WizVader/Smart-Energy-Monitor/Advance/Hardware/Comparator.asc

Cf1: cap; 1.592n
Cf2: cap; 1.592n
Cf3: cap; 1.592n
D1: diode
D2: diode
R1: res; 10k
R2: res; 10k
R3: res; 10k
R4: res; 10k
R5: res; 1k
R6: res; 500k
R7: res; 35.714k
R8: res; 1k
R9: res; 500k
R10: res; 35.714k
R11: res; 10k
R12: res; 330k
Rf1: res; 10k
Rf2: res; 10k
Rf3: res; 10k
U1: opamp2; LM324
U2: opamp2; LM324
U3: opamp2; LM324
U4: opamp2; LM324
V1: voltage; SINE(2.1 1 500); AC 1 0
V2: voltage; 5V
V3: voltage; 2.1
V4: voltage; 2.1
V5: voltage; 5
V6: voltage; 2.1
V7: voltage; 5
Named nets: 0, Vopamp, Vfilter, Vout, Voutput, 5V, Vzero, 2V1, Vvo
.tran 0 0.5 0 0.1m
.lib LM324.lib
Voltage Zero Crossing Detector Circuit using comparator
Notes:
- When Vvo > 2.1V, Vzero = 5V
When Vvo < 2.1V, Vzero = GND (Active high)
