WizVader/Smart-Energy-Monitor/Advance/Hardware/LevelShiftingAmplificationCircuit.asc

R1: res; 92.368k
R2: res; 92.368k
R3: res; 100k
R4: res; 100k
R5: res; 10k
R6: res; 10k
R7: res; 21.053k
R8: res; 21.053k
U1: opamp2; LM324
U2: opamp2; LM324
V2: voltage; 2.1V
Named nets: 0, 5V, Vvs, Vvo, 2V1, Vis, Vio
Differential Ampliflier for Voltage Sensor
Power/Signal Sources
Differential Amplifier for Current Sensor
