WizVader/Smart-Energy-Monitor/Advance/Hardware/rcfilter.asc

Cf1: cap; 1.592nF
Rf1: res; 10k
Named nets: Vio, 0, Vfilter
