WizVader/Smart-Energy-Monitor/Advance/Hardware/Regulator5V.asc

Cin1: cap; 47µ; Rser=0.001
Cout1: cap; 10µ; Rser=0.001
D1: diode; 1N4148
Reg1: LT1085-5
Rin1: res; 20
RL1: res; 50
V1: voltage; 5V
Named nets: 0, Vac, 5V, Vin, 5VDis
Notes: 
- Change net label 5VDis to 5V to use the DC regulator - In this case 
  the 5V net attached to V1 needs to be set to 5VDis to disconnect it
