WizVader/Smart-Energy-Monitor/Advance/Hardware/Sensor_Circtuits.asc

Lload1: ind; 4mH
Ra1: res; 498k
Rb1: res; 24k
Rload1: res; 94.026
Rs1: res; 0.5645
Vsupply1: voltage; SINE(0 21.778 500)
Named nets: 0, Vac, Vis, Vvs
Load 
(2.5VA-7.5VA)
Current Sens 
(Pmax=?)
