WizVader/Smart-Energy-Monitor/Advance/Hardware/Final Implementation (Prototype)/Team_09_Hardware.asc

C1: cap; 330p
C2: cap; 330p
C3: cap; 330p
C4: cap; 330p
C5: cap; 100n
C6: cap; 100n
C7: cap; 100n
Cf1: cap; 3.3n
Cf2: cap; 3.3n
Cin1: cap; 47µ; Rser=0.001
Cout1: cap; 10µ; Rser=0.001
D1: diode; 1N4148
Lload1: ind; 4mH
R1: res; 47k
R2: res; 47k
R3: res; 100k
R4: res; 100k
R5: res; 100k
R6: res; 100k
R7: res; 100k
R8: res; 100k
R9: res; 82
R11: res; 10k
R12: res; 280k
R13: res; 47k
R14: res; 33k
Ra1: res; 56k
Rb1: res; 2.7k
Reg1: LT1085-5
Rf1: res; 10k
Rf2: res; 10k
RL1: res; 56
Rload1: res; 94.028
Rreg: res; 27
Rs1: res; 1
Rs2: res; 1
U1: opamp2; LM324
U2: opamp2; LM324
U3: opamp2; LM324
U4: opamp2; LM324
U5: opamp2; LM324
V1: voltage; 5V
V3: voltage; SINE(0 0.5 500); AC .1 0
Vsupply1: voltage; SINE(0 19.8 500)
Named nets: 0, Vac, Vis, 5V, Vio, 2V1, Vvs, Vvf, Vif, 5VDis, Vsens, Vin, Vvo
AC Source, Load and Sensors
Load 
(2.5VA-7.5VA)
Current Sensor (Shunt)
Voltage Sensing (Voltage Divider)
*********************************************************
ELECTENG 209 - TEAM 09
This file contains the hardware for our project.
*********************************************************
.ac dec 30 1 1Meg
.lib LM324.lib
Simulation Commands
.tran 0 0.5 0 0.1m
.ic V(Vin)=8
Power/Signal Sources
Voltage Divider + Buffer
Voltage Filter
Current Filter
Comparator for Voltage Sensing
Comparator for Current Sensing
Regulator/ Power Supply
FILTERS
Current Sensing
Taken off the resistors from this comparator. 
Why? - Because The output (Vout) is A.(v+ -  v-). 
- In our case, Vvf is being fed into the v+ terminal 
- 2.1 offset (Vref) is being fed into the v-  terminal.
- When the Vvf crosses the Vref voltage line positively/negatively,
Vout will be equal to infinity (open loop gain) times the difference in terminal voltages,
- meaning the output will shoot up to positive/neative infinity respectively, but it will be limited to 
+5V (~3.5V) and 0V (~700mV) due to OPAMP power rails
;ac dec 30 1 1Meg
In our final PCB, we did not implement the 100nF capacitors
This is not implemented in the PCB
