WizVader/Smart-Energy-Monitor/Advance/Hardware/Final Implementation (Prototype)/Testing (delete later)/Final_Team_09_Hardware.asc

C1: cap; 0.45n
C2: cap; 0.45n
Cin1: cap; 47µ; Rser=0.001
Cout1: cap; 10µ; Rser=0.001
D1: diode; 1N4148
Lload1: ind; 4mH
R1: res; 100k
R2: res; 100k
R3: res; 100k
R4: res; 100k
Ra1: res; 56k
Rb1: res; 2.7k
Reg1: LT1085-5
Rin1: res; 20
RL1: res; 50
Rload1: res; 94.028
Rs1: res; 1
Rs2: res; 1
U1: opamp2; LM324
V1: voltage; 5V
V2: voltage; SINE(0 0.5 500); AC .1 0
V3: voltage; 2.1
Vsupply1: voltage; SINE(0 19.79 500)
Named nets: 0, 5VDis, Vsens, Vac, Vis, Vvs, 5V, Vin, 2V1
*********************************************************
ELECTENG 209 - TEAM 09
This file contains the hardware for our project.
*********************************************************
.ac dec 30 1 1Meg
.lib LM324.lib
Simulation Commands
;tran 0 0.5 0 0.1m
.ic V(Vin)=8
Power/Signal Sources
AC Source, Load and Sensors
Load 
(2.5VA-7.5VA)
Current Sensor (Shunt)
Regulator / Power Supply
.tran 0 0.5 0 0.1m
