WizVader/Smart-Energy-Monitor/Advance/Software/Team09_Final_Implementation/Team09_Final_Implementation/Display.h

/*
 * Display.h
 *
 * Created: 6/10/2023 3:56:58 pm
 *Author: Charanjeet, Sai Kiran, Kristelle, Pratham
 */ 


#ifndef DISPLAY_H_
#define DISPLAY_H_


// Add functions used in Display.c
void init_display();

void displayCurrent();

void displayVoltage();

void displayPower();

void seperate_and_load_characters(uint32_t number, uint8_t decimal_pos);

void send_next_character_to_display();

int float_to_integer(float toDisplay);

#endif /* DISPLAY_H_ */
