WizVader/Smart-Energy-Monitor/Advance/Software/Team09_Final_Implementation/Team09_Final_Implementation/Timer0.h

/*
 * Timer0.h
 *
 * Created: 12/10/2023 1:42:01 pm
 *  Author: Charanjeet, Sai Kiran, Kristelle, Pratham
 */ 


#ifndef TIMER0_H_
#define TIMER0_H_

// Functions used in Timer0.c
void timer0_init();



#endif /* TIMER0_H_ */
